giltesa/Tetris-DX-PCB/3. Documentation/Board Development/Board/IceBoy/jan-spakula-1_01_front.jpg

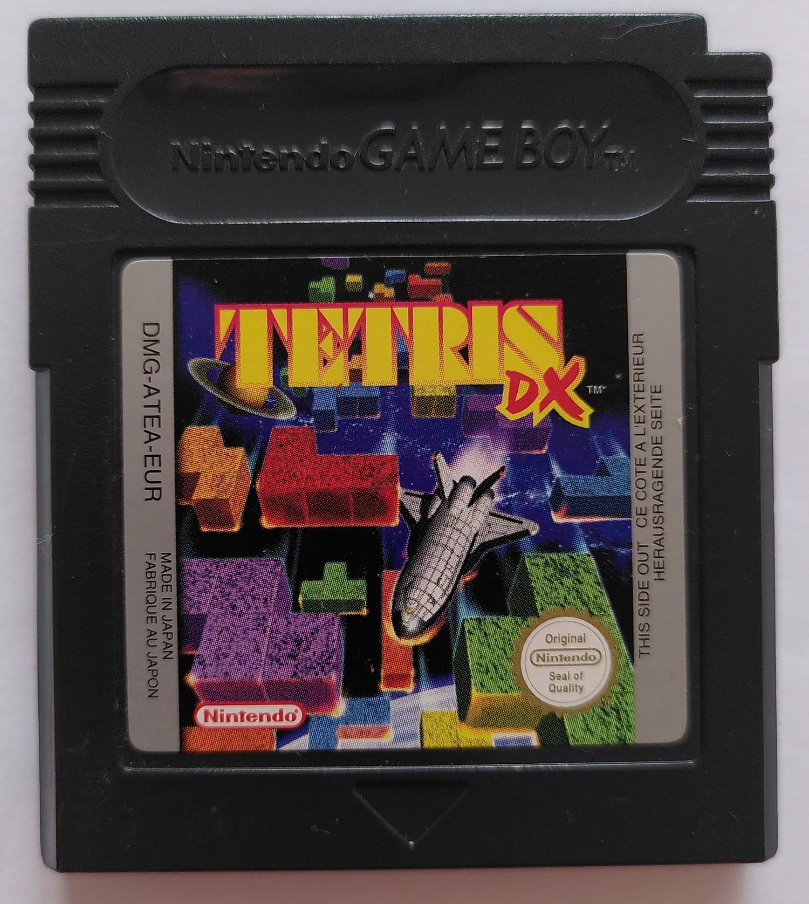
3. Documentation/Board Development/Board/IceBoy/jan-spakula-1_01_front.jpg
