giltesa/Tetris-DX-PCB/3. Documentation/Board Development/Board/PCB Scans/Top.jpg

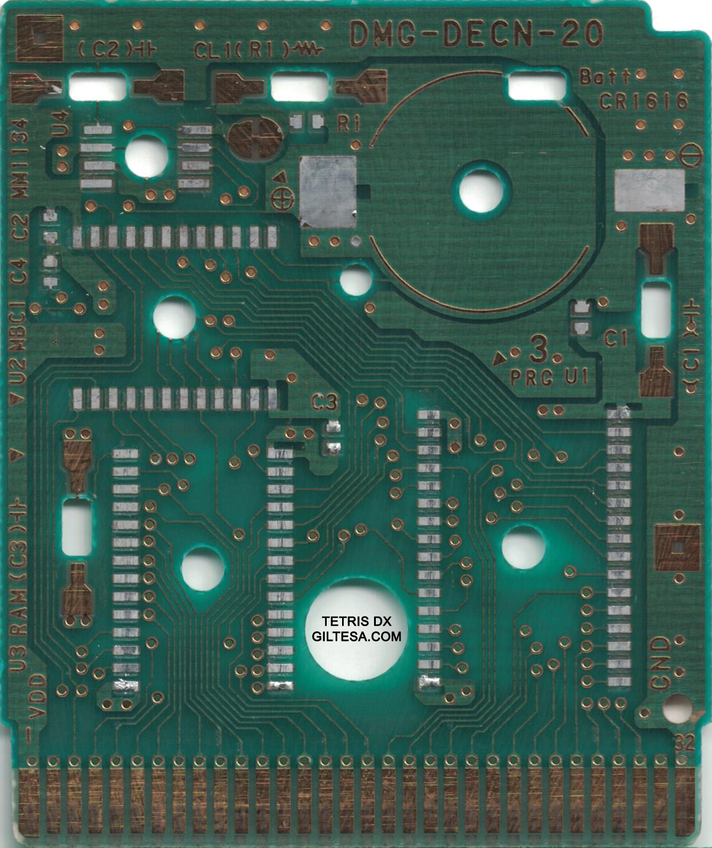
3. Documentation/Board Development/Board/PCB Scans/Top.jpg
