giltesa/Tetris-DX-PCB/3. Documentation/Datasheet/Game Boy Color card shell/Game Boy card shell/S50be32216ba94c5dbb75d0d31687d7b6k.png

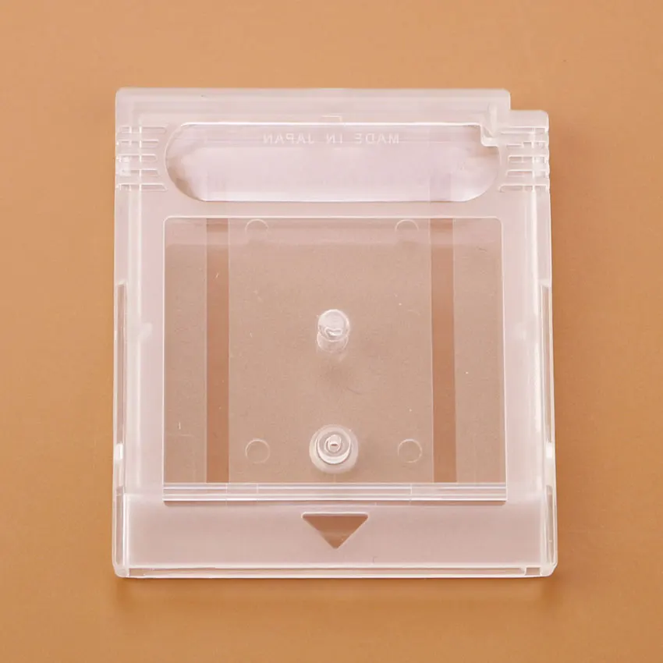
3. Documentation/Datasheet/Game Boy Color card shell/Game Boy card shell/S50be32216ba94c5dbb75d0d31687d7b6k.png
