giltesa/Tetris-DX-PCB/3. Documentation/Datasheet/Game Boy Color card shell/Game Boy Color card shell/S69fde07da0c248d798be7f6e69b6b89dx.png

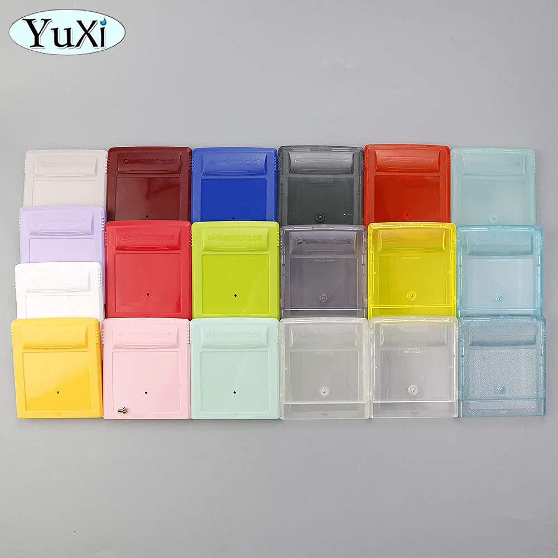
3. Documentation/Datasheet/Game Boy Color card shell/Game Boy Color card shell/S69fde07da0c248d798be7f6e69b6b89dx.png
